norayr-noro/LoRa_board-myway/photosss/PCB_lora(2d).png

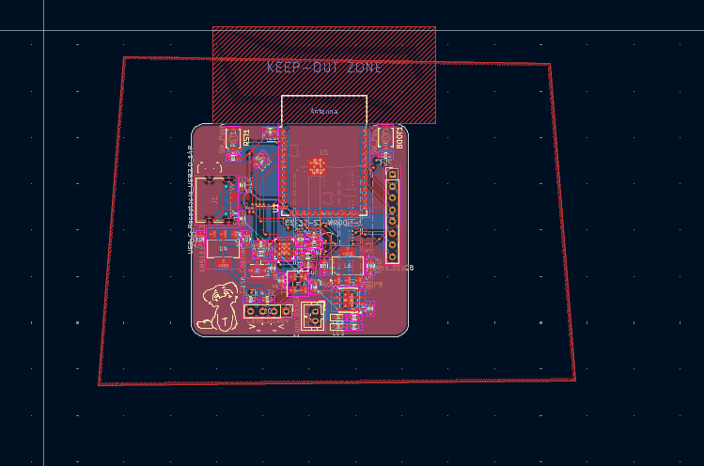
photosss/PCB_lora(2d).png
